Ariamelon/Cantaloupe/Images/Photo1.jpg

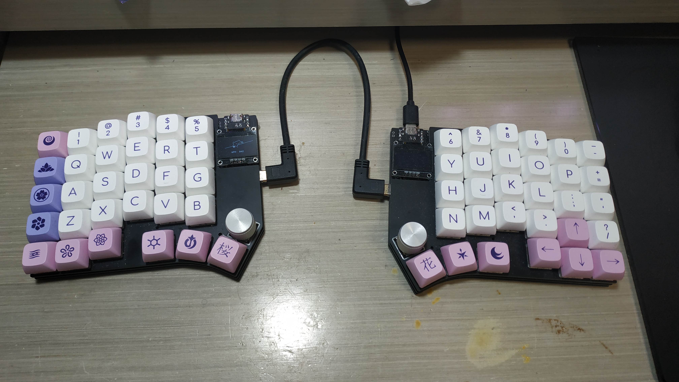
Images/Photo1.jpg
